dremeier/BMW_N57_Oilpressure_over_Wifi/docs/IMG_7752.JPG

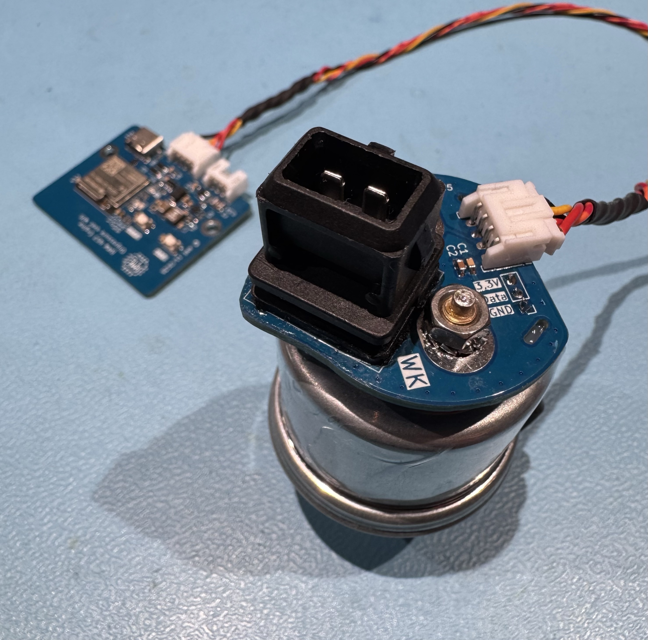
docs/IMG_7752.JPG
